OrcaTheWhale/The-TCGMat/StepFiles/Part Studio 1 - BMat5O.step

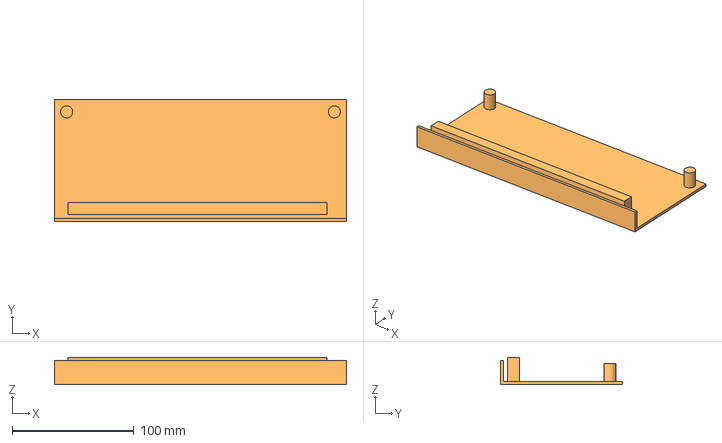
[picture p19: CAD file, 2026-05-20]
StepFiles/Part Studio 1 - BMat5O.step
240.0 x 100.0 x 22.5 mm
